elkayem/ESP_NIXIE/images/20190120-0001.jpg

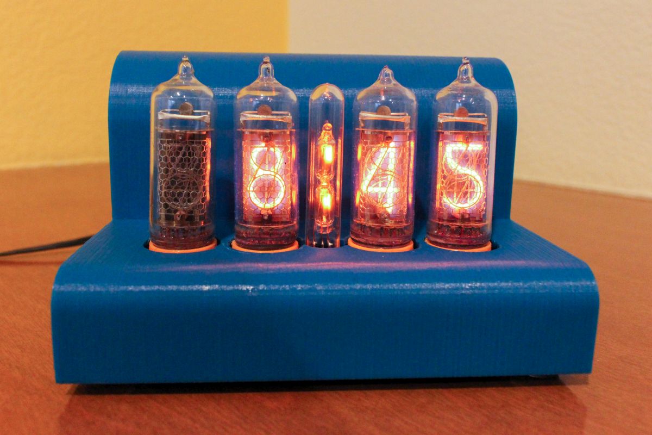
images/20190120-0001.jpg
