elkayem/ESP_NIXIE/images/IMG_1246.JPG

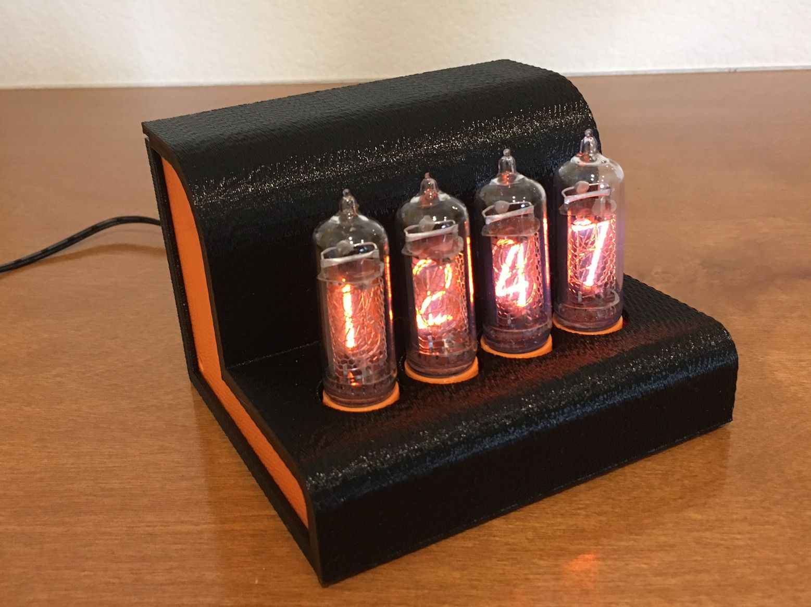
images/IMG_1246.JPG
