elkayem/ESP_NIXIE/images/IMG_1248.JPG

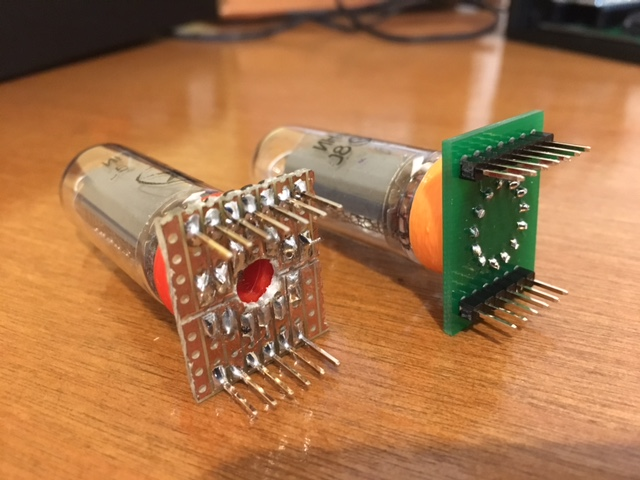
images/IMG_1248.JPG
