elkayem/ESP_NIXIE/images/IMG_3056.jpg

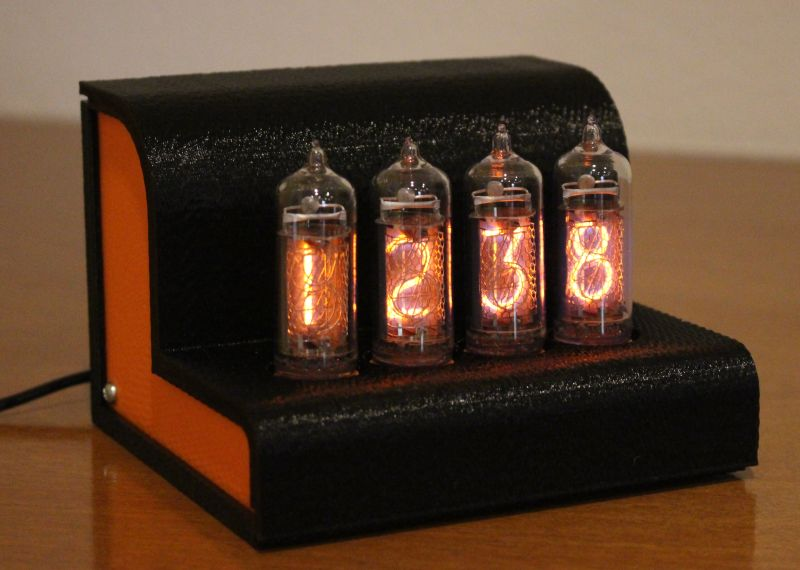
images/IMG_3056.jpg
