elkayem/ESP_NIXIE/images/IMG_3060.jpg

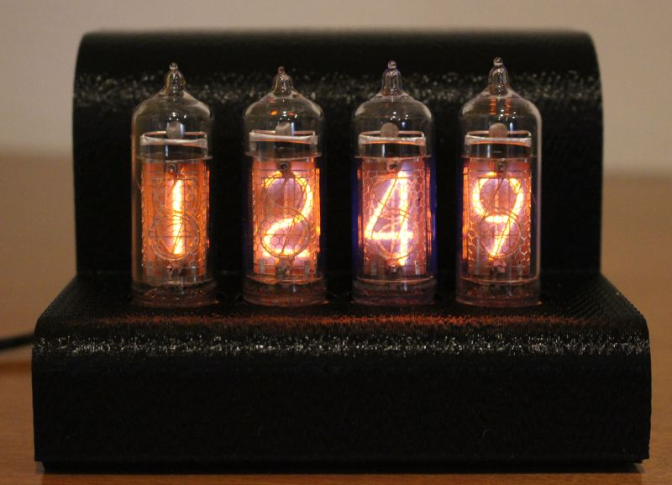
images/IMG_3060.jpg
